SerialSniffyHeck3r/AIO-Instrument-Practicing-Device-TUNION-/Codes/Core/Inc/notch.h

#pragma once

#include "notch.h"
#include <string.h>
#include <math.h>
#include <stdio.h>
#include "Util.h"
#include "LCD16X2.h"
#include "LCD16X2_cfg.h"
#include "main.h"



#include "arm_math.h"
#include <stdint.h>

#ifdef __cplusplus
extern "C" {
#endif
